jacobjuneau6/SPACENOTIFY/3.png

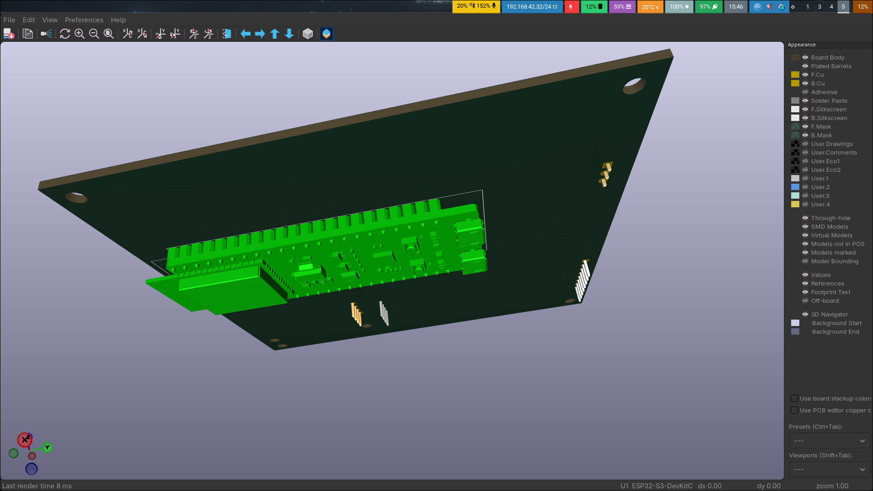
3.png
