jacobjuneau6/SPACENOTIFY/v1/symbols/KiCad-SSD1306-128x64-0.1/oled-128-x-64-display-1.snapshot.15/OLED Display 128x64 Solidworks.JPG

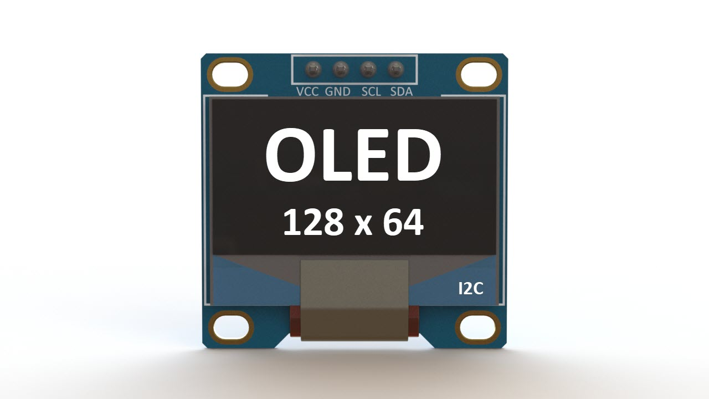
v1/symbols/KiCad-SSD1306-128x64-0.1/oled-128-x-64-display-1.snapshot.15/OLED Display 128x64 Solidworks.JPG
